dchwebb/Ampelope/Ampelope/src/initialisation.cpp

#include "initialisation.h"

// Settings for 24MHz (dev board) and 8MHz (production) crystal
// 24MHz / 6(M) * 85(N) / 2(R) = 170MHz
//  8MHz / 2(M) * 85(N) / 2(R) = 170MHz
#if CRYSTAL_24MHZ
#define PLL_M 0b101		// 0101: PLLM = 6
#else
#define PLL_M 0b001		// 0001: PLLM = 2
#endif
#define PLL_N 85
#define PLL_R 0			//  00: PLLR = 2, 01: PLLR = 4, 10: PLLR = 6, 11: PLLR = 8
#define PLL_P 2


void SystemClock_Config(void) {
	// See page 236 for clock configuration
	RCC->APB2ENR |= RCC_APB2ENR_SYSCFGEN;		// SYSCFG + COMP + VREFBUF + OPAMP clock enable
	RCC->APB1ENR1 |= RCC_APB1ENR1_PWREN;		// Enable Power Control clock
	PWR->CR5 &= ~PWR_CR5_R1MODE;				// Select the Range 1 boost mode

	RCC->CR |= RCC_CR_HSEON;					// HSE ON
	while ((RCC->CR & RCC_CR_HSERDY) == 0);		// Wait till HSE is ready

	// Configure PLL
	RCC->PLLCFGR = (PLL_M << RCC_PLLCFGR_PLLM_Pos) | (PLL_N << RCC_PLLCFGR_PLLN_Pos) | (PLL_P << RCC_PLLCFGR_PLLPDIV_Pos) | (PLL_R << RCC_PLLCFGR_PLLR_Pos) | (RCC_PLLCFGR_PLLSRC_HSE);
	RCC->CR |= RCC_CR_PLLON;					// Enable the main PLL
	RCC->PLLCFGR = RCC_PLLCFGR_PLLREN;			// Enable PLL R (drives AHB clock)
	while ((RCC->CR & RCC_CR_PLLRDY) == 0);		// Wait till the main PLL is ready

	// Configure Flash prefetch and wait state. NB STM32G431 is a category 2 device (128KB flash in 1 bank)
	FLASH->ACR |= FLASH_ACR_LATENCY_4WS | FLASH_ACR_PRFTEN;
	FLASH->ACR &= ~FLASH_ACR_LATENCY_1WS;

	// The system clock must be divided by 2 using the AHB prescaler before switching to a higher system frequency.
	RCC->CFGR |= RCC_CFGR_HPRE_DIV2;			// HCLK = SYSCLK / 2
	RCC->CFGR |= RCC_CFGR_SW_PLL;				// Select the main PLL as system clock source

	// Wait till the main PLL is used as system clock source
	while ((RCC->CFGR & (uint32_t)RCC_CFGR_SWS ) != RCC_CFGR_SWS_PLL);

	// Reset the AHB clock (previously divided by 2) and set APB clocks
	RCC->CFGR &= ~RCC_CFGR_HPRE_Msk;
	RCC->CFGR |= RCC_CFGR_PPRE1_DIV1;			// PCLK1 = HCLK / 1 (APB1)
	RCC->CFGR |= RCC_CFGR_PPRE2_DIV1;			// PCLK2 = HCLK / 1 (APB2)
}


void InitSysTick()
{
	SysTick_Config(SystemCoreClock / SYSTICK);		// gives 1ms
	NVIC_SetPriority(SysTick_IRQn, 0);
}

void InitDAC()
{
	// Configure 4 DAC outputs PA4 and PA5 are regular DAC1 buffered outputs; PA2 and PB1 are DAC3 via OpAmp1 and OpAmp3 (Manual p.789)

	RCC->AHB2ENR |= RCC_AHB2ENR_GPIOAEN;			// Enable GPIO Clock
	RCC->AHB2ENR |= RCC_AHB2ENR_GPIOBEN;			// Enable GPIO Clock
	RCC->AHB2ENR |= RCC_AHB2ENR_DAC1EN;				// Enable DAC Clock
	RCC->AHB2ENR |= RCC_AHB2ENR_DAC3EN;				// Enable DAC Clock

	DAC1->MCR &= ~DAC_MCR_MODE1_Msk;				// Set to normal mode: DAC channel1 is connected to external pin with Buffer enabled
	DAC1->CR |= DAC_CR_EN1;							// Enable DAC using PA4 (DAC_OUT1)

	DAC1->MCR &= ~DAC_MCR_MODE2_Msk;				// Set to normal mode: DAC channel2 is connected to external pin with Buffer enabled
	DAC1->CR |= DAC_CR_EN2;							// Enable DAC using PA5 (DAC_OUT2)

	// output triggered with DAC->DHR12R1 = x;

	// Opamp for DAC3 Channel 1: Follower configuration mode - output on PA2
	DAC3->MCR |= DAC_MCR_MODE1_0 | DAC_MCR_MODE1_1;	// 011: DAC channel1 is connected to on chip peripherals with Buffer disabled
	DAC3->CR |= DAC_CR_EN1;							// Enable DAC

	OPAMP1->CSR |= OPAMP_CSR_VMSEL;					// 11: Opamp_out connected to OPAMPx_VINM input
	OPAMP1->CSR |= OPAMP_CSR_VPSEL;					// 11: DAC3_CH1  connected to OPAMP1 VINP input
	OPAMP1->CSR |= OPAMP_CSR_OPAMPxEN;				// Enable OpAmp: voltage on pin OPAMPx_VINP is buffered to pin OPAMPx_VOUT (PA2)

	// Opamp for DAC3 Channel 2: Follower configuration mode - output on PB1
	// NB According to manual p.790 this should only work on category 3/4 devices and STM32G431 is category 2, but tested working
	DAC3->MCR |= DAC_MCR_MODE2_0 | DAC_MCR_MODE2_1;	// 011: DAC channel2 is connected to on chip peripherals with Buffer disabled
	DAC3->CR |= DAC_CR_EN2;							// Enable DAC

	OPAMP3->CSR |= OPAMP_CSR_VMSEL;					// 11: Opamp_out connected to OPAMPx_VINM input
	OPAMP3->CSR |= OPAMP_CSR_VPSEL;					// 11: DAC3_CH2  connected to OPAMP1 VINP input
	OPAMP3->CSR |= OPAMP_CSR_OPAMPxEN;				// Enable OpAmp: voltage on pin OPAMPx_VINP is buffered to pin OPAMPx_VOUT (PB1)

}


void InitIO()
{
	// MODER 00: Input mode, 01: General purpose output mode, 10: Alternate function mode, 11: Analog mode (reset state)

	RCC->AHB2ENR |= RCC_AHB2ENR_GPIOAEN;			// reset and clock control - advanced high performance bus - GPIO port A
	RCC->AHB2ENR |= RCC_AHB2ENR_GPIOBEN;			// reset and clock control - advanced high performance bus - GPIO port B
	RCC->AHB2ENR |= RCC_AHB2ENR_GPIOCEN;			// reset and clock control - advanced high performance bus - GPIO port C

	GPIOB->MODER &= ~GPIO_MODER_MODER13;			// configure PB13 gate 1 input
	GPIOB->MODER &= ~GPIO_MODER_MODER14;			// configure PB14 gate 2 input
	GPIOB->MODER &= ~GPIO_MODER_MODER15;			// configure PB15 gate 3 input
	GPIOC->MODER &= ~GPIO_MODER_MODER6;				// configure PC6  gate 4 input

	// NB PB6 is used in USB Power delivery and by default has a pull down to ground - disable in the PWR register (datasheet p.60 note 5)
	PWR->CR3 |= PWR_CR3_UCPD_DBDIS;

	GPIOB->MODER &= ~GPIO_MODER_MODER5;				// configure PB5  Env 1 Short input
	GPIOB->MODER &= ~GPIO_MODER_MODER6;				// configure PB6  Env 1 tremolo input*
	GPIOB->MODER &= ~GPIO_MODER_MODER3;				// configure PB3  Env 2 Short input
	GPIOB->MODER &= ~GPIO_MODER_MODER4;				// configure PB4  Env 2 tremolo input
	GPIOC->MODER &= ~GPIO_MODER_MODER10;			// configure PC10 Env 3 Short input
	GPIOC->MODER &= ~GPIO_MODER_MODER12;			// configure PC12 Env 3 tremolo input
	GPIOB->MODER &= ~GPIO_MODER_MODER12;			// configure PB12 Env 4 Short input
	GPIOA->MODER &= ~GPIO_MODER_MODER15;			// configure PA15 Env 4 tremolo input

	GPIOB->PUPDR |= GPIO_PUPDR_PUPDR5_0;			// configure PB5  Env 1 Pull-up
	GPIOB->PUPDR |= GPIO_PUPDR_PUPDR6_0;			// configure PB6  Env 1 Pull-up
	GPIOB->PUPDR |= GPIO_PUPDR_PUPDR3_0;			// configure PB3  Env 2 Pull-up
	GPIOB->PUPDR |= GPIO_PUPDR_PUPDR4_0;			// configure PB4  Env 2 Pull-up
	GPIOC->PUPDR |= GPIO_PUPDR_PUPDR10_0;			// configure PC10 Env 3 Pull-up
	GPIOC->PUPDR |= GPIO_PUPDR_PUPDR12_0;			// configure PC12 Env 3 Pull-up
	GPIOB->PUPDR |= GPIO_PUPDR_PUPDR12_0;			// configure PB12 Env 4 Pull-up
	GPIOA->PUPDR |= GPIO_PUPDR_PUPDR15_0;			// configure PA15 Env 4 Pull-up

	GPIOA->MODER &= ~GPIO_MODER_MODER9;				// configure PA9 clock input
	GPIOB->MODER &= ~GPIO_MODER_MODER9_1;			// configure PB9 debug out
}


//	Setup Timer 3 on an interrupt to trigger sample output
void InitEnvTimer() {
	RCC->APB1ENR1 |= RCC_APB1ENR1_TIM3EN;			// Enable Timer 3
	TIM3->PSC = 34;									// Set prescaler
	TIM3->ARR = 103; 								// Set auto reload register - 170Mhz / 33 / 103 = ~50kHz

	TIM3->DIER |= TIM_DIER_UIE;						// DMA/interrupt enable register
	NVIC_EnableIRQ(TIM3_IRQn);
	NVIC_SetPriority(TIM3_IRQn, 0);					// Lower is higher priority

	TIM3->CR1 |= TIM_CR1_CEN;
	TIM3->EGR |= TIM_EGR_UG;						//  Re-initializes counter and generates update of registers
}


void InitAdcPins(ADC_TypeDef* ADC_No, std::initializer_list<uint8_t> channels) {
	uint8_t sequence = 1;

	for (auto channel: channels) {
		// Set conversion sequence to order ADC channels are passed to this function
		if (sequence < 5) {
			ADC_No->SQR1 |= channel << ((sequence) * 6);
		} else if (sequence < 10) {
			ADC_No->SQR2 |= channel << ((sequence - 5) * 6);
		} else if (sequence < 15) {
			ADC_No->SQR3 |= channel << ((sequence - 10) * 6);
		} else {
			ADC_No->SQR4 |= channel << ((sequence - 15) * 6);
		}

		// 000: 3 cycles, 001: 15 cycles, 010: 28 cycles, 011: 56 cycles, 100: 84 cycles, 101: 112 cycles, 110: 144 cycles, 111: 480 cycles
		if (channel < 10)
			ADC_No->SMPR1 |= 0b010 << (3 * channel);
		else
			ADC_No->SMPR2 |= 0b010 << (3 * (channel - 10));

		sequence++;
	}
}


void InitADC(volatile uint16_t* ADC_array)
{
	// Initialize Clocks
	RCC->AHB1ENR |= RCC_AHB1ENR_DMA1EN;
	RCC->AHB1ENR |= RCC_AHB1ENR_DMAMUX1EN;
	RCC->AHB2ENR |= RCC_AHB2ENR_ADC12EN;
	RCC->CCIPR |= RCC_CCIPR_ADC12SEL_1;				// 00: pll2_p_ck (default), 01: pll3_r_ck clock, 10: per_ck clock

	DMA1_Channel1->CCR &= ~DMA_CCR_EN;
	DMA1_Channel1->CCR |= DMA_CCR_CIRC;				// Circular mode to keep refilling buffer
	DMA1_Channel1->CCR |= DMA_CCR_MINC;				// Memory in increment mode
	DMA1_Channel1->CCR |= DMA_CCR_PSIZE_0;			// Peripheral size: 8 bit; 01 = 16 bit; 10 = 32 bit
	DMA1_Channel1->CCR |= DMA_CCR_MSIZE_0;			// Memory size: 8 bit; 01 = 16 bit; 10 = 32 bit
	DMA1_Channel1->CCR |= DMA_CCR_PL_0;				// Priority: 00 = low; 01 = Medium; 10 = High; 11 = Very High

	DMA1->IFCR = 0x3F << DMA_IFCR_CGIF1_Pos;		// clear all five interrupts for this stream

	DMAMUX1_Channel0->CCR |= 5; 					// DMA request MUX input 5 = ADC1 (See p.427)
	DMAMUX1_ChannelStatus->CFR |= DMAMUX_CFR_CSOF0; // Channel 1 Clear synchronization overrun event flag

	ADC1->CR &= ~ADC_CR_DEEPPWD;					// Deep power down: 0: ADC not in deep-power down	1: ADC in deep-power-down (default reset state)
	ADC1->CR |= ADC_CR_ADVREGEN;					// Enable ADC internal voltage regulator

	// Wait until voltage regulator settled
	volatile uint32_t wait_loop_index = (SystemCoreClock / (100000UL * 2UL));
	while (wait_loop_index != 0UL) {
		wait_loop_index--;
	}
	while ((ADC1->CR & ADC_CR_ADVREGEN) != ADC_CR_ADVREGEN) {}

	ADC12_COMMON->CCR |= ADC_CCR_CKMODE;			// adc_hclk/4 (Synchronous clock mode)
	ADC1->CFGR |= ADC_CFGR_CONT;					// 1: Continuous conversion mode for regular conversions
	ADC1->CFGR |= ADC_CFGR_OVRMOD;					// Overrun Mode 1: ADC_DR register is overwritten with the last conversion result when an overrun is detected.
	ADC1->CFGR |= ADC_CFGR_DMACFG;					// 0: DMA One Shot Mode selected, 1: DMA Circular Mode selected
	ADC1->CFGR |= ADC_CFGR_DMAEN;					// Enable ADC DMA

	// For scan mode: set number of channels to be converted
	ADC1->SQR1 |= (ADC_BUFFER_LENGTH - 1);

	// Start calibration
	ADC1->CR &= ~ADC_CR_ADCALDIF;					// Calibration in single ended mode
	ADC1->CR |= ADC_CR_ADCAL;
	while ((ADC1->CR & ADC_CR_ADCAL) == ADC_CR_ADCAL) {};


	/*--------------------------------------------------------------------------------------------
	Configure ADC Channels to be converted:
	0	PC0 ADC12_IN6		Env1 Attack
	1	PC1 ADC12_IN7		Env1 Decay
	2	PC2 ADC12_IN8		Env1 Sustain
	3	PC3 ADC12_IN9		Env1 Release

	4	PA0 ADC12_IN1		Env2 Attack
	5	PA1 ADC12_IN2		Env2 Decay
	6	PA3 ADC1_IN4		Env2 Sustain
	7	PB0 ADC1_IN15		Env2 Release

	8	PB11 ADC12_IN14		LFO Speed
	*/

	InitAdcPins(ADC1, {6, 7, 8, 9, 1, 2, 4, 15, 14});


	// Enable ADC
	ADC1->CR |= ADC_CR_ADEN;
	while ((ADC1->ISR & ADC_ISR_ADRDY) == 0) {}

	DMAMUX1_ChannelStatus->CFR |= DMAMUX_CFR_CSOF0; // Channel 1 Clear synchronization overrun event flag
	DMA1->IFCR = 0x3F << DMA_IFCR_CGIF1_Pos;		// clear all five interrupts for this stream

	DMA1_Channel1->CNDTR |= ADC_BUFFER_LENGTH;		// Number of data items to transfer (ie size of ADC buffer)
	DMA1_Channel1->CPAR = (uint32_t)(&(ADC1->DR));	// Configure the peripheral data register address 0x40022040
	DMA1_Channel1->CMAR = (uint32_t)(ADC_array);	// Configure the memory address (note that M1AR is used for double-buffer mode) 0x24000040

	DMA1_Channel1->CCR |= DMA_CCR_EN;				// Enable DMA and wait
	wait_loop_index = (SystemCoreClock / (100000UL * 2UL));
	while (wait_loop_index != 0UL) {
		wait_loop_index--;
	}

	ADC1->CR |= ADC_CR_ADSTART;						// Start ADC
}


void InitCordic()
{
	RCC->AHB1ENR |= RCC_AHB1ENR_CORDICEN;
}


/*
//	Setup Timer 9 to count clock cycles for coverage profiling
void InitCoverageTimer() {
	RCC->APB2ENR |= RCC_APB2ENR_TIM9EN;				// Enable Timer
	TIM9->PSC = 100;
	TIM9->ARR = 65535;

	TIM9->DIER |= TIM_DIER_UIE;						// DMA/interrupt enable register
	NVIC_EnableIRQ(TIM1_BRK_TIM9_IRQn);
	NVIC_SetPriority(TIM1_BRK_TIM9_IRQn, 2);		// Lower is higher priority

}

//	Setup Timer 5 to count time between bounces
void InitDebounceTimer() {
	RCC->APB1ENR |= RCC_APB1ENR_TIM5EN;				// Enable Timer
	TIM5->PSC = 10000;
	TIM5->ARR = 65535;
}

*/
