dchwebb/Ampelope/Ampelope/src/SerialHandler.cpp

#include "SerialHandler.h"
#include "Envelope.h"

#include <stdio.h>
#include <cmath>		// for cordic test

extern Envelopes envelopes;

int32_t SerialHandler::ParseInt(const std::string cmd, const char precedingChar, int low = 0, int high = 0) {
	int32_t val = -1;
	int8_t pos = cmd.find(precedingChar);		// locate position of character preceding
	if (pos >= 0 && std::strspn(cmd.substr(pos + 1).c_str(), "0123456789-") > 0) {
		val = stoi(cmd.substr(pos + 1));
	}
	if (high > low && (val > high || val < low)) {
		usb->SendString("Must be a value between " + std::to_string(low) + " and " + std::to_string(high) + "\r\n");
		return low - 1;
	}
	return val;
}

float SerialHandler::ParseFloat(const std::string cmd, const char precedingChar, float low = 0.0, float high = 0.0) {
	float val = -1.0f;
	int8_t pos = cmd.find(precedingChar);		// locate position of character preceding
	if (pos >= 0 && std::strspn(cmd.substr(pos + 1).c_str(), "0123456789.") > 0) {
		val = stof(cmd.substr(pos + 1));
	}
	if (high > low && (val > high || val < low)) {
		usb->SendString("Must be a value between " + std::to_string(low) + " and " + std::to_string(high) + "\r\n");
		return low - 1.0f;
	}
	return val;
}

SerialHandler::SerialHandler(USBHandler& usbObj)
{
	usb = &usbObj;

	// bind the usb's CDC caller to the CDC handler in this class
	usb->cdcDataHandler = std::bind(&SerialHandler::Handler, this, std::placeholders::_1, std::placeholders::_2);
}



// Check if a command has been received from USB, parse and action as required
bool SerialHandler::Command()
{
	char buf[50];

	if (!CmdPending) {
		return false;
	}

	// Provide option to switch to USB DFU mode - this allows the MCU to be programmed with STM32CubeProgrammer in DFU mode
	if (state == serialState::dfuConfirm) {
		if (ComCmd.compare("y\n") == 0 || ComCmd.compare("Y\n") == 0) {
			usb->SendString("Switching to DFU Mode ...\r\n");
			uint32_t old = SysTickVal;
			while (SysTickVal < old + 100) {};		// Give enough time to send the message
			//bootloader.BootDFU();
		} else {
			state = serialState::pending;
			usb->SendString("Upgrade cancelled\r\n");
		}

	} else if (ComCmd.compare("info\n") == 0) {		// Print diagnostic information

		usb->SendString("Mountjoy Ampelope v1.0 - Current Settings:\r\n\r\n"
				"Envelope Times:" + std::string(envelopes.envelope[0].longADSR ? "long" : "short") + "\r\n");

	} else if (ComCmd.compare("help\n") == 0) {

		usb->SendString("Mountjoy Ampelope\r\n"
				"\r\nSupported commands:\r\n"
				"info        -  Show diagnostic information\r\n"
				"l/s         -  Long or Short envelope times\r\n"
				"lfo         -  Tremolo LFO on/off\r\n"
				"\r\n"
#if (USB_DEBUG)
				"usbdebug    -  Start USB debugging\r\n"
				"\r\n"
#endif
		);

#if (USB_DEBUG)
	} else if (ComCmd.compare("usbdebug\n") == 0) {				// Configure gate LED
		USBDebug = true;
		usb->SendString("Press link button to dump output\r\n");
#endif

	} else if (ComCmd.compare("lfo\n") == 0) {				// LFO on/off
//		envelope.tremolo = !envelope.tremolo;
//		usb->SendString("LFO " + std::string(envelope.tremolo ? "on" : "off") + "\r\n");

	} else if (ComCmd.compare("l\n") == 0) {				// Long envelope times
		//envelope.longTimes = true;

	} else if (ComCmd.compare("s\n") == 0) {				// Short envelope times
		//envelope.longTimes = false;

/*	} else if (ComCmd.compare(0, 9, "mdlength:") == 0) {		// Modulated Delay length
		uint16_t val = ParseInt(ComCmd, ':', 1, 65535);
		if (val > 0) {
			delay.modOffsetMax = val;
			delay.modOffset[left] = delay.modOffsetMax / 2;
			delay.modOffset[right] = delay.modOffsetMax / 2;
			config.SaveConfig();
		}
		usb->SendString("Modulated delay length set to: " + std::to_string(delay.modOffsetMax) + "\r\n");
*/

	} else {
		usb->SendString("Unrecognised command: " + ComCmd + "Type 'help' for supported commands\r\n");
	}

	CmdPending = false;
	return true;
}


void SerialHandler::Handler(uint8_t* data, uint32_t length)
{
	static bool newCmd = true;
	if (newCmd) {
		ComCmd = std::string(reinterpret_cast<char*>(data), length);
		newCmd = false;
	} else {
		ComCmd.append(reinterpret_cast<char*>(data), length);
	}
	if (*ComCmd.rbegin() == '\r')
		*ComCmd.rbegin() = '\n';

	if (*ComCmd.rbegin() == '\n') {
		CmdPending = true;
		newCmd = true;
	}

}
